saikoLED/TeensyLED/Examples/TeensyLED/TeensyLED.ino

//**************************************************************************
//
// TeensyLED Controller
// Copyright Brian Neltner 2015
// Version 0.2 - April 18, 2015
//
// This provides a basic library and example code for interacting
// with a RGBW LED light using Hue, Saturation, and Intensity (HSI)
// mode. This version has been updated to match the pinout of the RGBW
// driver board provided in the associated Eagle Design files included
// in this repository.
//
// Software Features:
// - HSI to RGBW library for interacting with LED sources.
// - PID based fader that follows a random walk through colorspace.
// - Outline (totally untested) start of DMX receiving software.
//
// This file is part of TeensyLED Controller.
//
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
//***************************************************************************

#include "LEDs.h"
#include <DmxReceiver.h>

#define propgain 0.001

// Redpin, Greenpin, Bluepin, Whitepin, Resolution, Frequency.
RGBWLamp lamp(6, 22, 23, 9, 16, 183.106);

// Define DMX Device.
DmxReceiver dmx;
IntervalTimer dmxTimer;

// Global target hue and saturation for follower.
float targethue;
float targetsaturation;

void setup() {
  Serial.begin(115200);
  float S[3] = {0, 1, 1};
  float D[3];
  
  while(1) {
    Hsi2Rgb(&D[0], &D[1], &D[2], S[0], S[1], S[2]);
    Serial.println(String(S[0]) + ", " + String(S[1]) + ", " + String(S[2]) + " -> " + String(D[0]) + ", " + String(D[1]) + ", " + String(D[2]));
    delay(1000);
  }
  
  lamp.begin();
  dmx.begin();
  dmxTimer.begin(dmxTimerISR, 1000);
  
  targethue = 0;
  targetsaturation = 1.0;
  
  // Initialize light at the target hue, no brightness, fully saturated.
  lamp.setHue(targethue);
  lamp.setIntensity(0);
  lamp.setSaturation(targetsaturation);
  lamp.setColor();
  
  // Startup Routine.
  while (lamp.getIntensity() < 1) {
    lamp.setIntensity(lamp.getIntensity()+0.001);
    updatetargethue();
    updatetargetsaturation();
    lamp.setHue(lamp.getHue() + propgain*(targethue - lamp.getHue()));
    lamp.setSaturation(lamp.getSaturation() + propgain*(targetsaturation - lamp.getSaturation()));
    lamp.setColor();
    delay(1);
  }
}

elapsedMillis elapsed;

void loop() {
//  if (dmx.newFrame()) {
//    Serial.println("New DMX Frame.");
//  }
  
  if (elapsed > 5) {
    updatetargethue();
    updatetargetsaturation();
    lamp.setHue(lamp.getHue() + propgain*(targethue - lamp.getHue()));
    lamp.setSaturation(lamp.getSaturation() + propgain*(targetsaturation - lamp.getSaturation()));
    lamp.setColor();
    elapsed -= 5;
  }
}

void updatetargethue() {
  targethue += (rand()%360-180)*0.01;
  targethue = fmod(targethue+360, 360);
}

void updatetargetsaturation() {
  targetsaturation += (rand()%10000-5000)*0.00001;
  targetsaturation = targetsaturation>0.5?(targetsaturation<1?targetsaturation:1):0.5;
}

void dmxTimerISR(void) {
  dmx.bufferService();
}

void Hsi2Rgb(float *R, float *G, float *B, float H, float S, float I)
{
  H -= 360*floor(H/360);
	
  if(H < 120)
  {
    *B = I*(1 - S);
    *R = I*(1 + S*cos(H*(M_PI/180))/cos((60 - H)*(M_PI/180)));
    *G = 3*I - *R - *B;
  }
  else if(H < 240)
  {
    H -= 120;
    *R = I*(1 - S);
    *G = I*(1 + S*cos(H*(M_PI/180))/cos((60 - H)*(M_PI/180)));
    *B = 3*I - *R - *G;
  }
  else
  {
    H -= 240;
    *G = I*(1 - S);
    *B = I*(1 + S*cos(H*(M_PI/180))/cos((60 - H)*(M_PI/180)));
    *R = 3*I - *G - *B;
  }
}
